janknieling/volkszaehler-yport/pictures/yport-new5.jpg

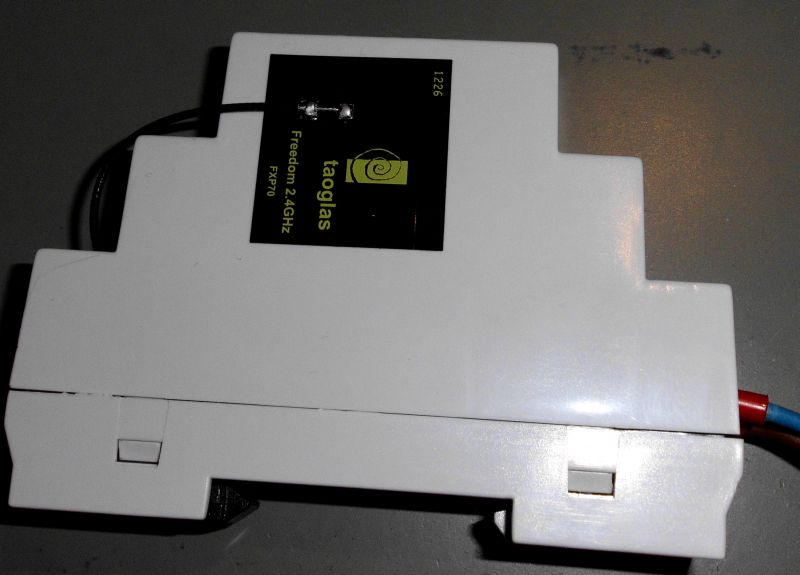
pictures/yport-new5.jpg
