janknieling/volkszaehler-yport/pictures/yport-new8.jpg

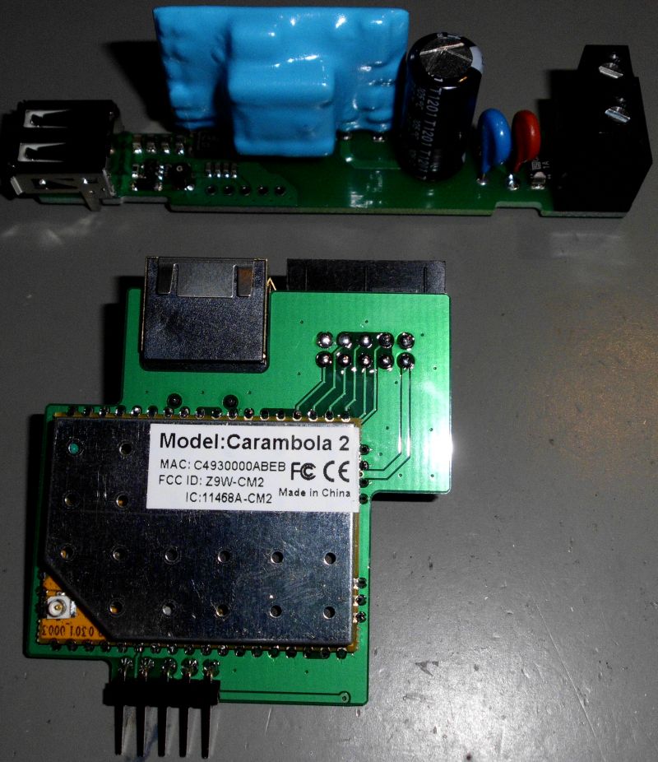
pictures/yport-new8.jpg
