janknieling/volkszaehler-yport/pictures/yport_bestueckungsplanplan_bot_oberteil.png

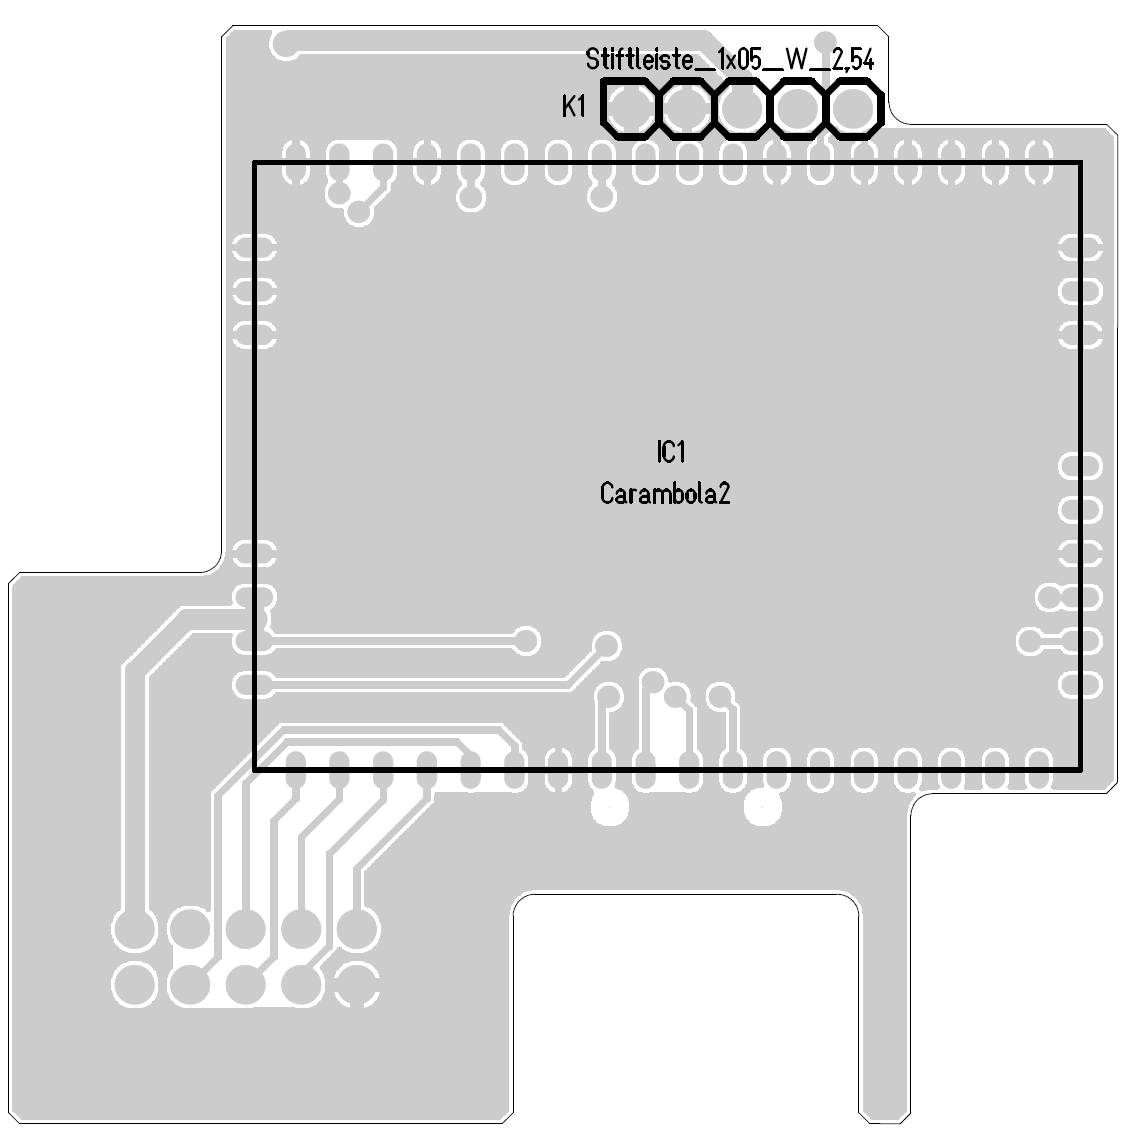
pictures/yport_bestueckungsplanplan_bot_oberteil.png
