janknieling/volkszaehler-yport/pictures/yport_bestueckungsplanplan_top_oberteil.png

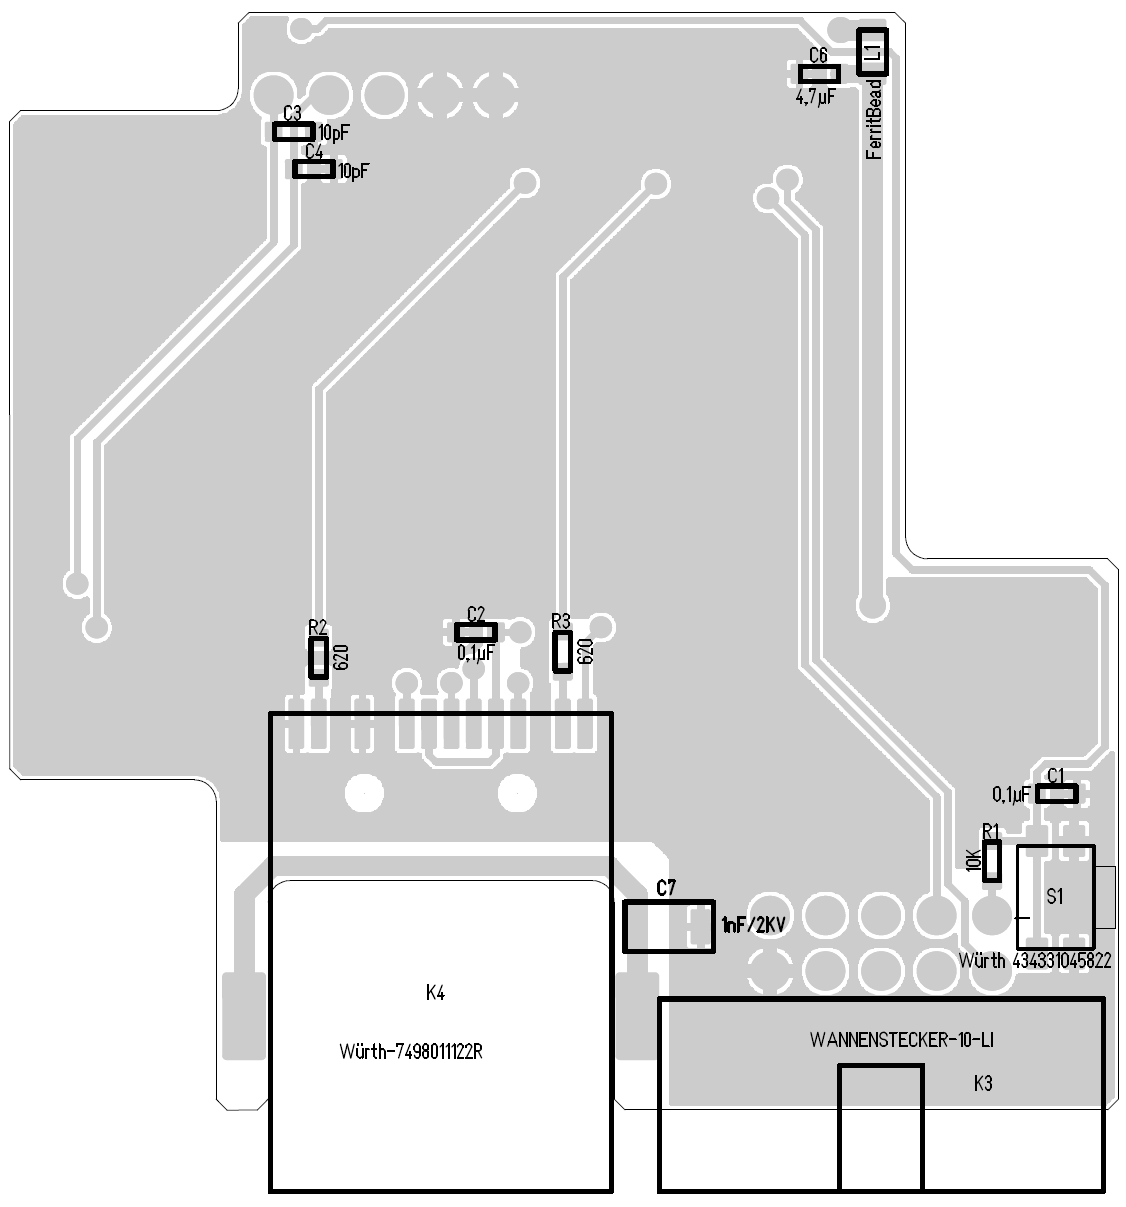
pictures/yport_bestueckungsplanplan_top_oberteil.png
